Hung-Chi970104/cpu_from_scratch/assets/adder.png

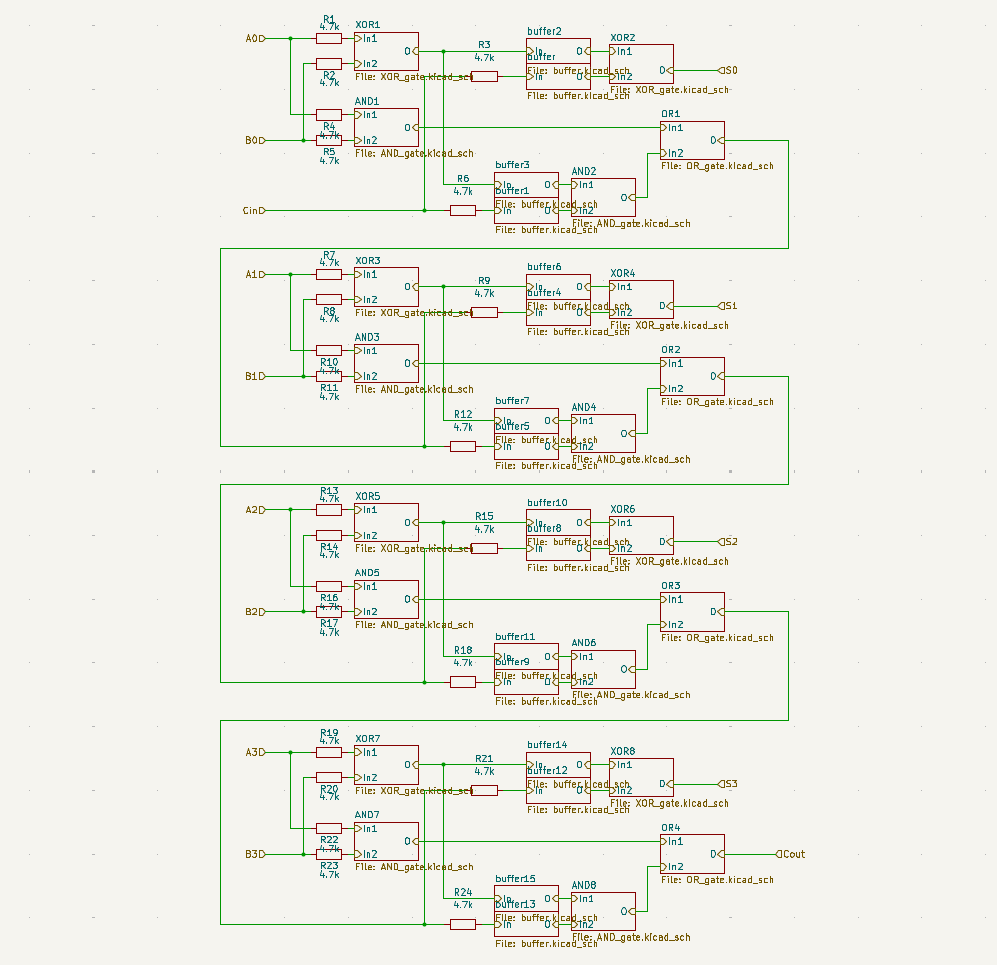
assets/adder.png
