Hung-Chi970104/cpu_from_scratch/assets/NAND.JPG

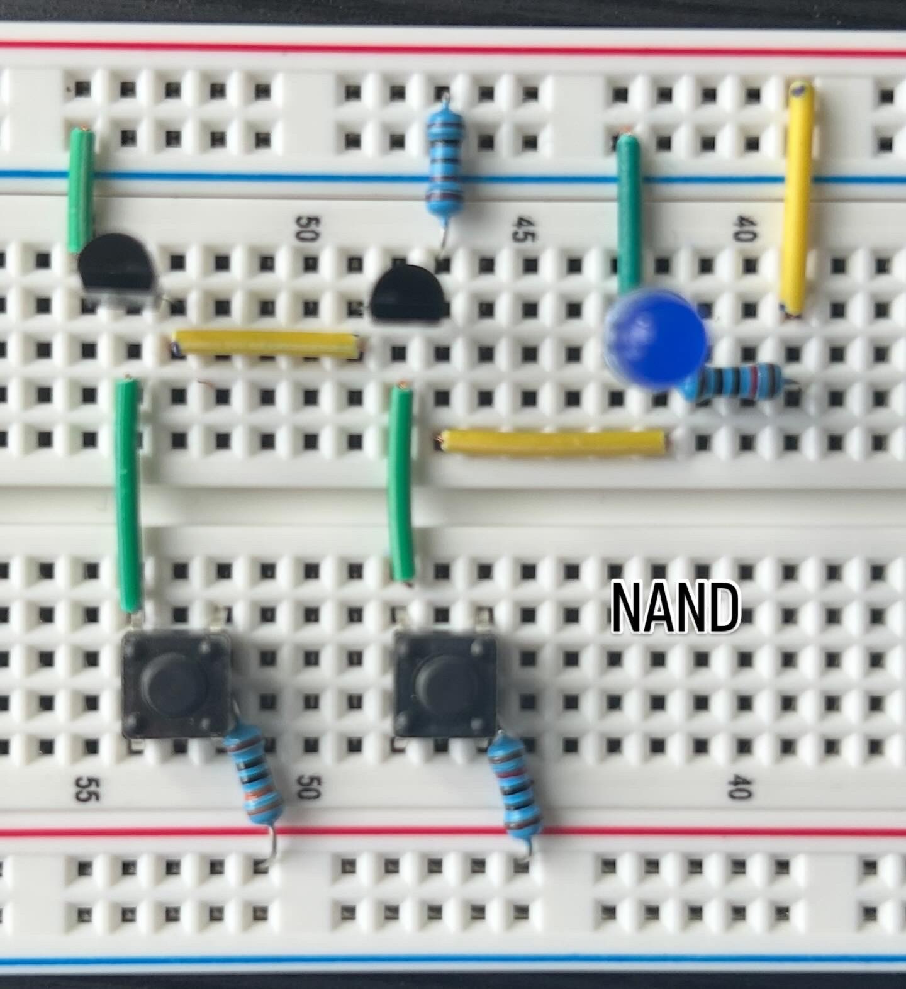
assets/NAND.JPG
