Hung-Chi970104/cpu_from_scratch/assets/NOR.JPG

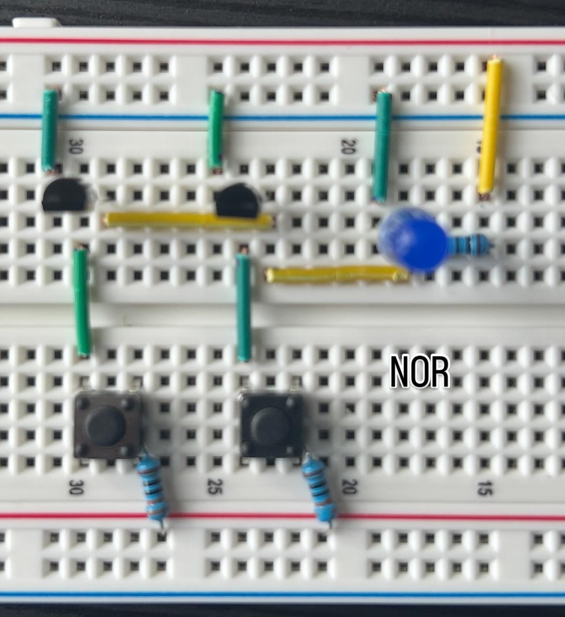
assets/NOR.JPG
