Hung-Chi970104/cpu_from_scratch/assets/Prototype.jpeg

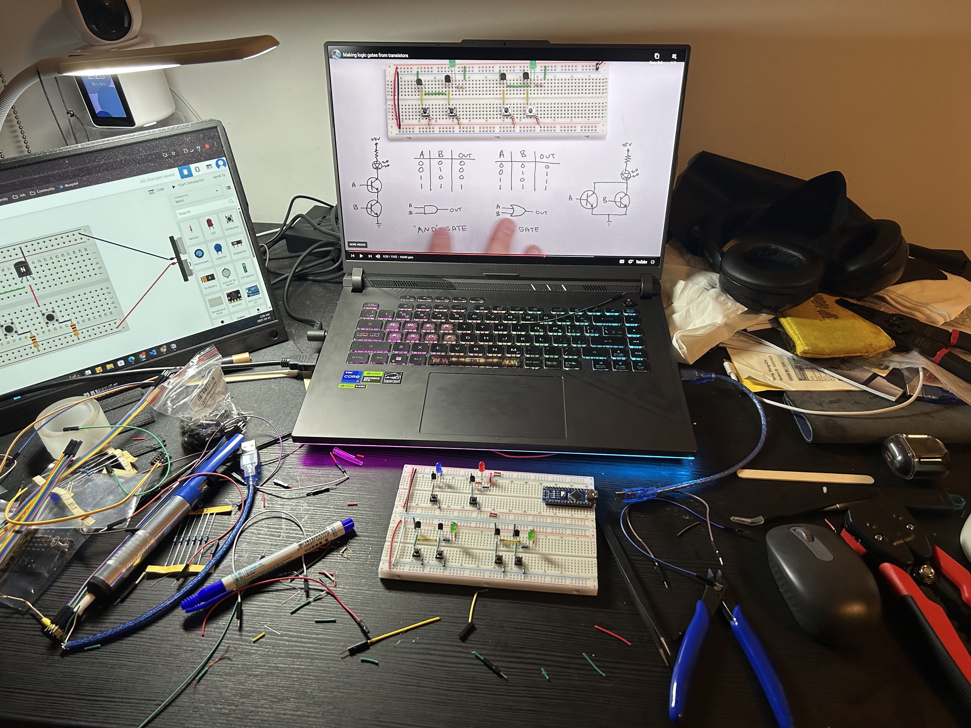
assets/Prototype.jpeg
