Hung-Chi970104/cpu_from_scratch/assets/xor.png

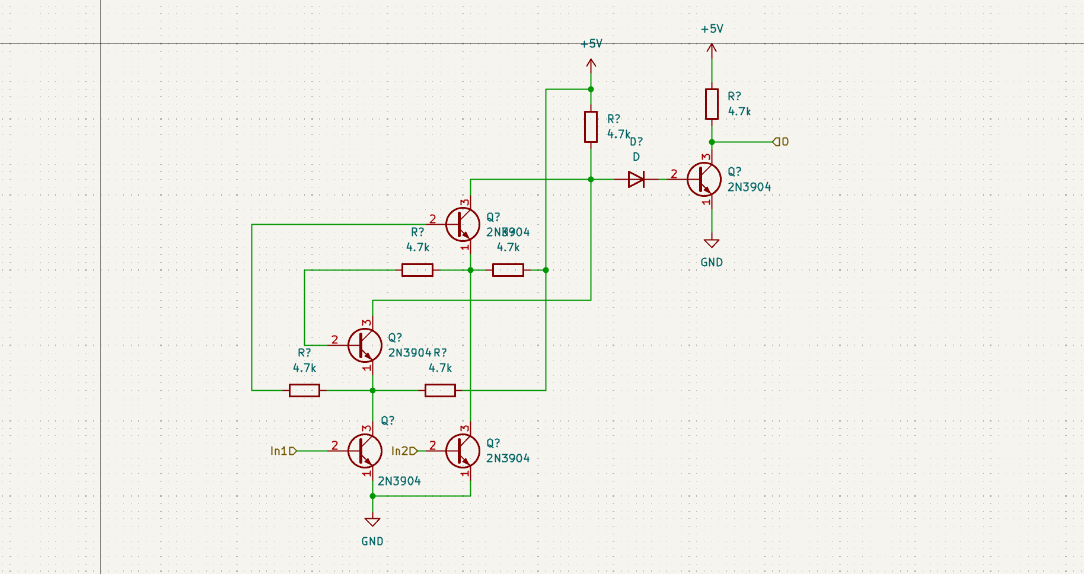
assets/xor.png
